phampaul07/pomodoro-cube/firmware/pet_sheet.bmp

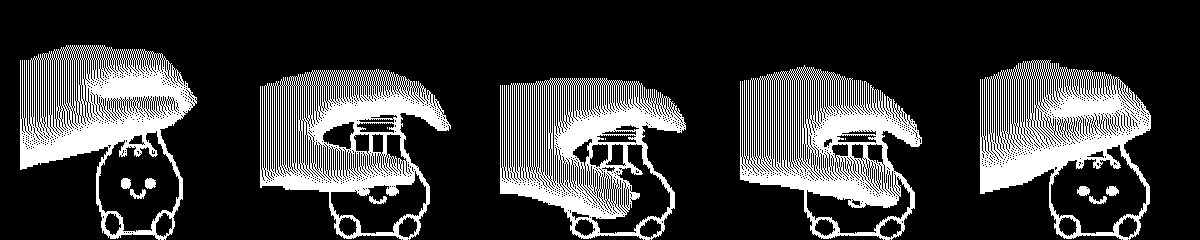
firmware/pet_sheet.bmp
