phampaul07/pomodoro-cube/images/IMG_2748.jpg

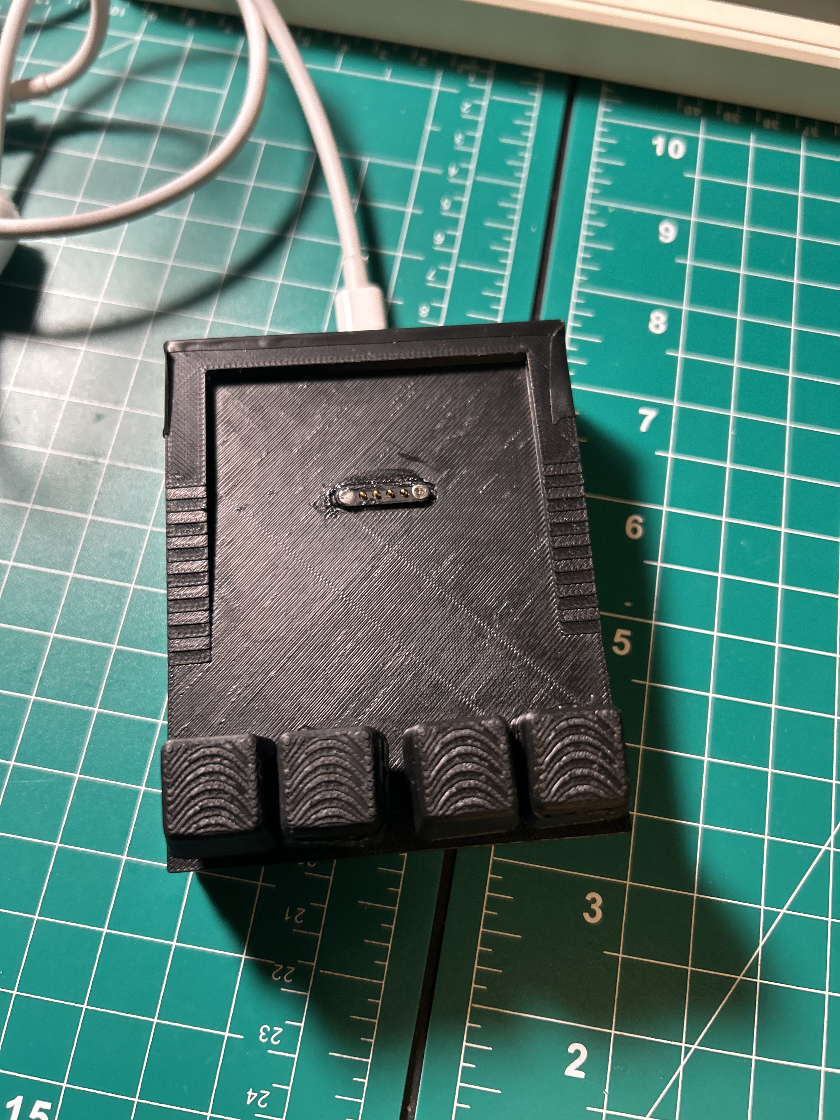
images/IMG_2748.jpg
