phampaul07/pomodoro-cube/images/IMG_2749.jpg

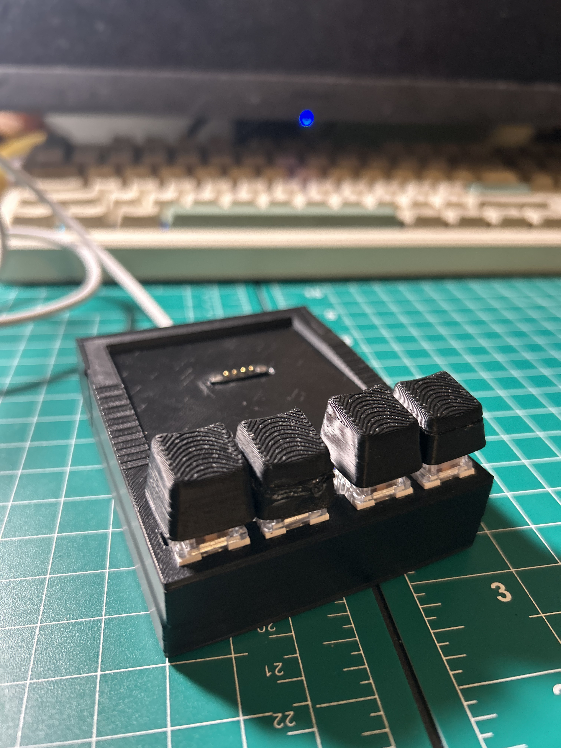
images/IMG_2749.jpg
