phampaul07/pomodoro-cube/images/IMG_2750.jpg

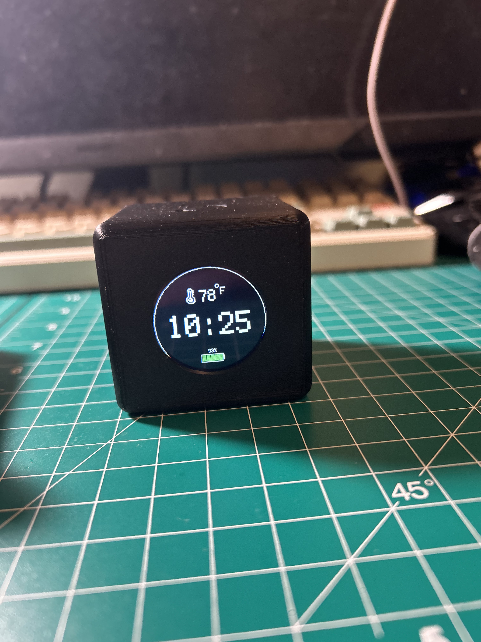
images/IMG_2750.jpg
