phampaul07/pomodoro-cube/images/IMG_2751.jpg

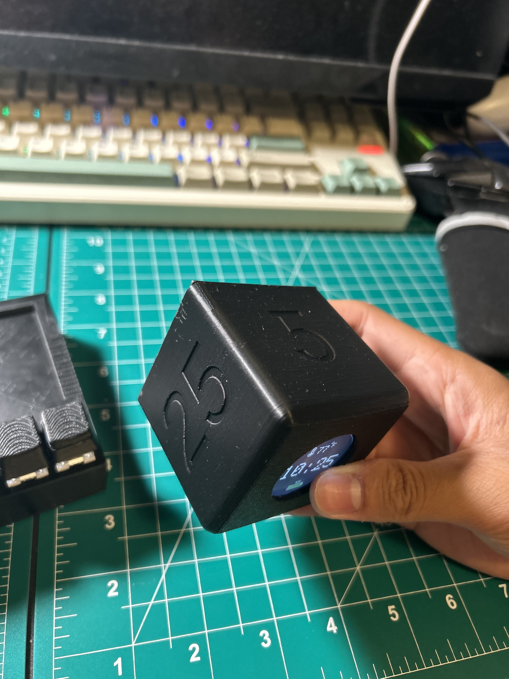
images/IMG_2751.jpg
