phampaul07/pomodoro-cube/images/IMG_2752.jpg

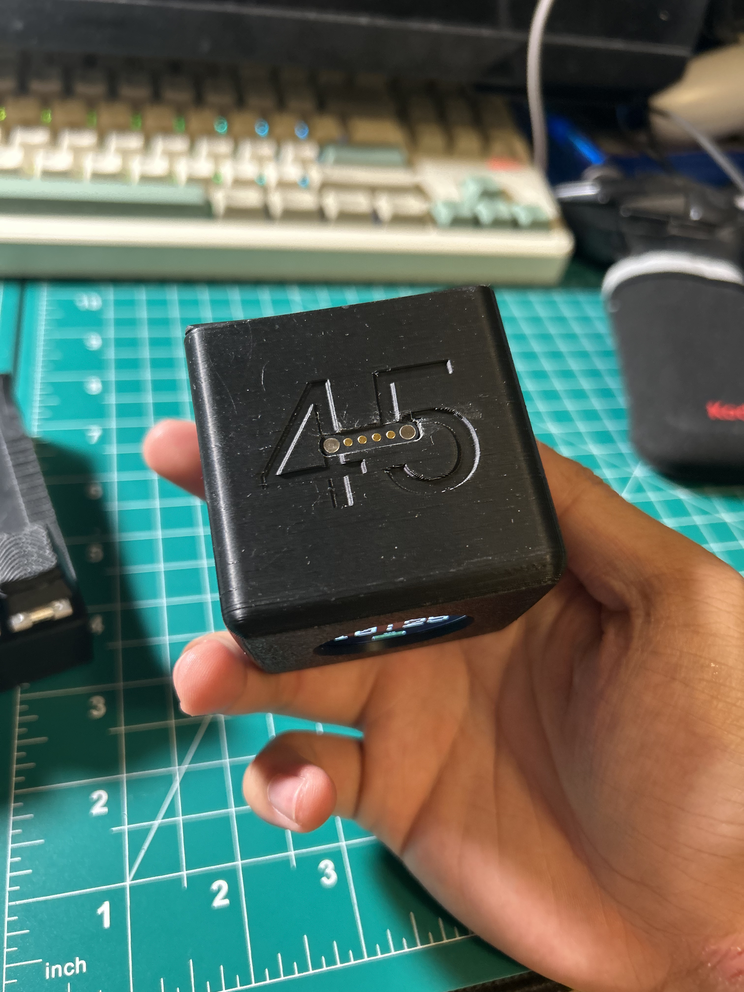
images/IMG_2752.jpg
