phampaul07/pomodoro-cube/images/IMG_2753.jpg

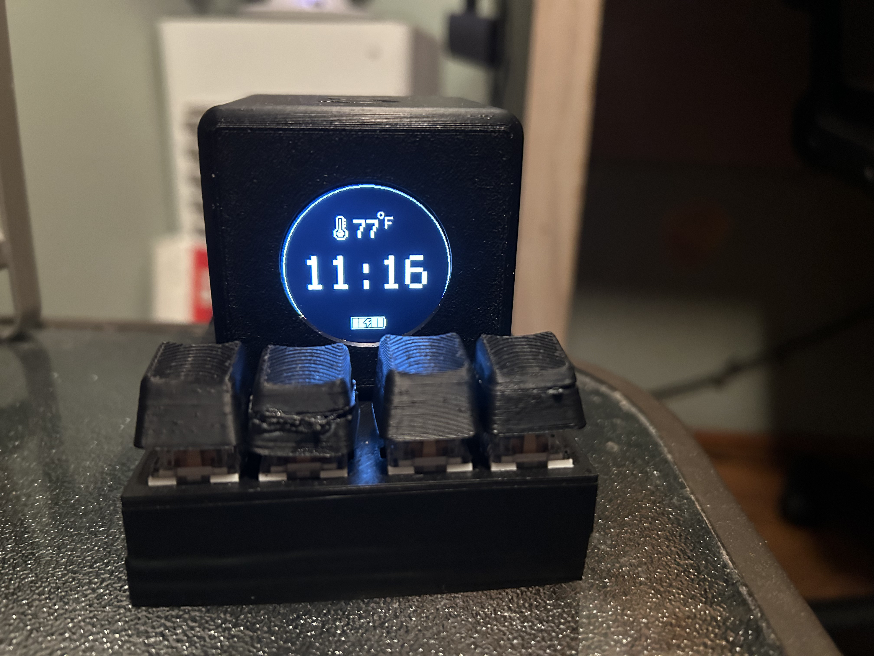
images/IMG_2753.jpg
