phampaul07/pomodoro-cube/images/IMG_2754.jpg

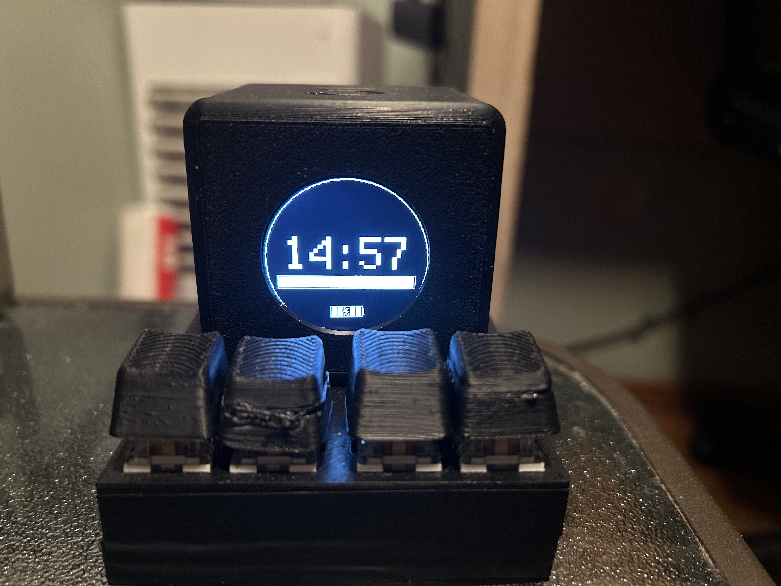
images/IMG_2754.jpg
