phampaul07/pomodoro-cube/images/IMG_2756.jpg

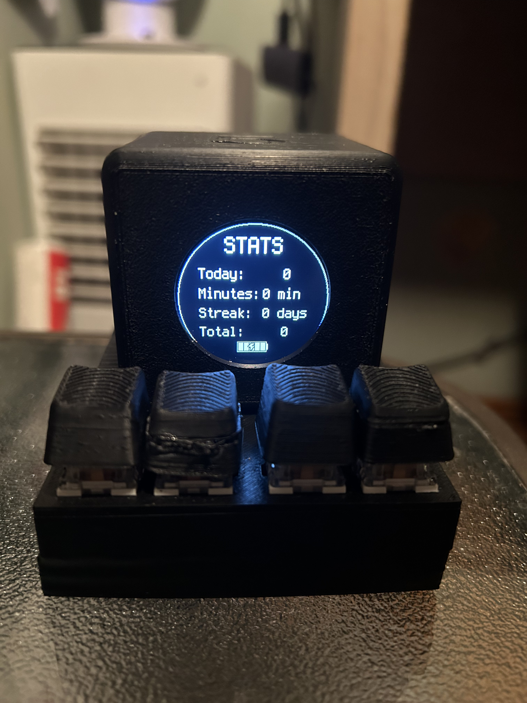
images/IMG_2756.jpg
