phampaul07/pomodoro-cube/firmware/accel_test.py

import time
import board
import busio
import adafruit_mpu6050

# Open the physical hardware bridge (SCL first, SDA second)
i2c = busio.I2C(board.D5, board.D4)
mpu = adafruit_mpu6050.MPU6050(i2c)

print("--- MPU-6050 SENSOR ONLINE ---")

while True:
    accel_x, accel_y, accel_z = mpu.acceleration
    print(f"X_acc: {accel_x:.2f} | Y_accel: {accel_y:.2f} | Z_accel: {accel_z:.2f}")
    
    time.sleep(0.2)
    
